SuperHouse/WMC/Images/2019-10-28 19.47.27.jpg

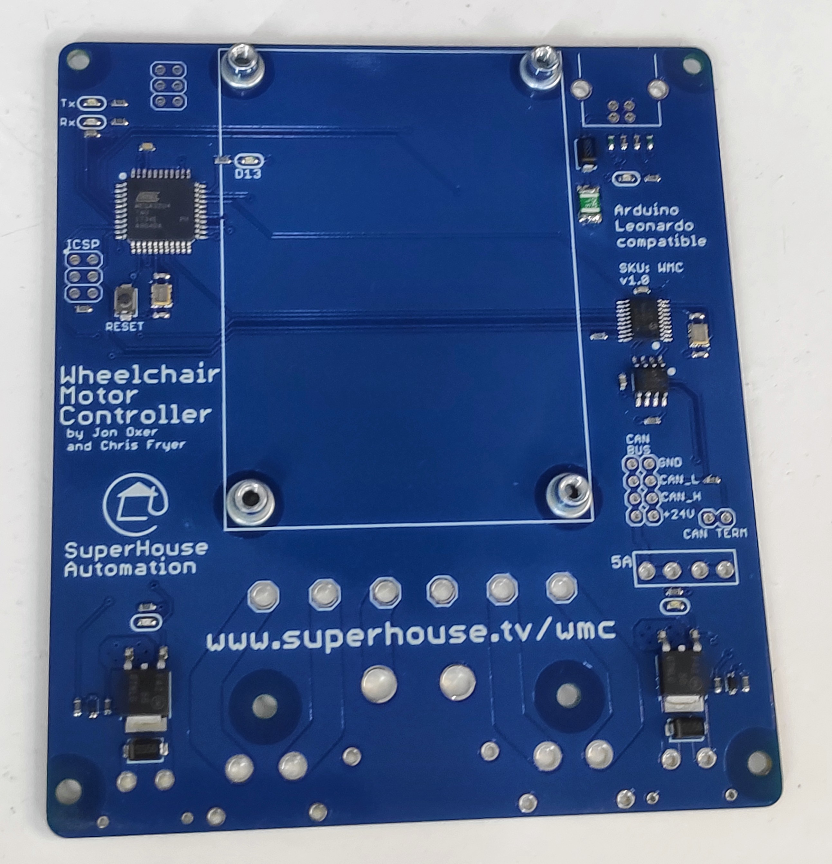
Images/2019-10-28 19.47.27.jpg
