SuperHouse/WMC/Images/2019-10-28 22.34.21.jpg

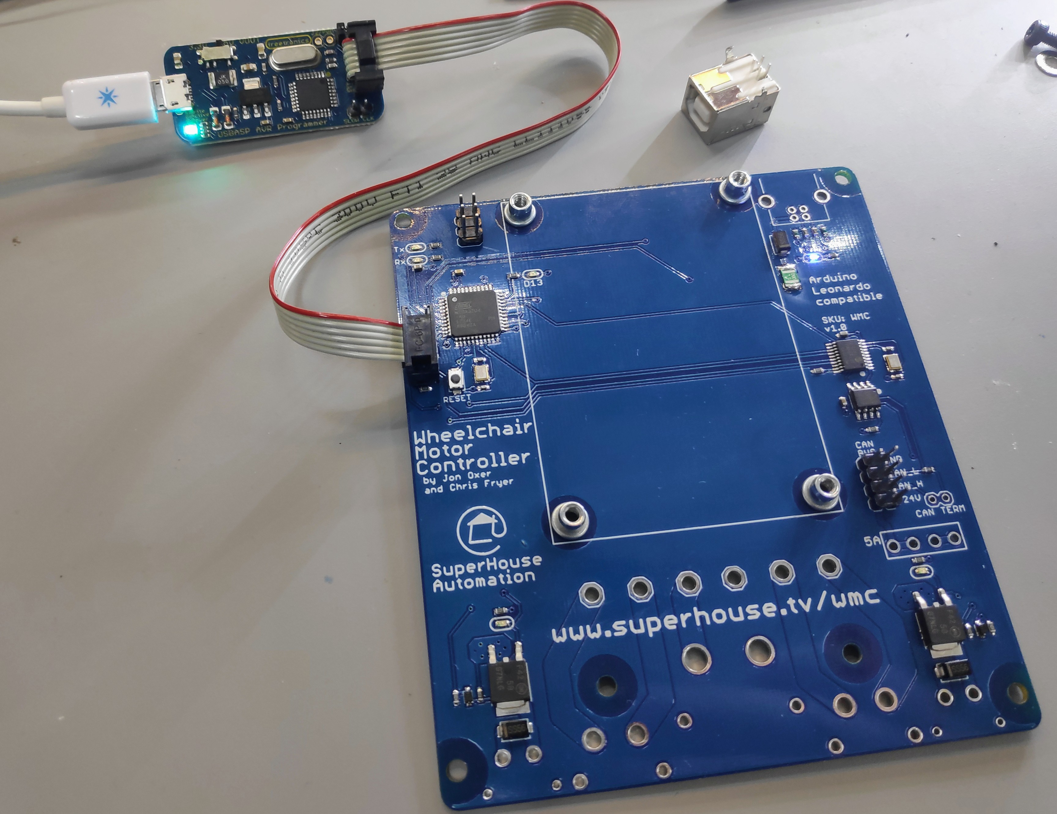
Images/2019-10-28 22.34.21.jpg
