SuperHouse/WMC/Images/2019-10-29 12.58.57.jpg

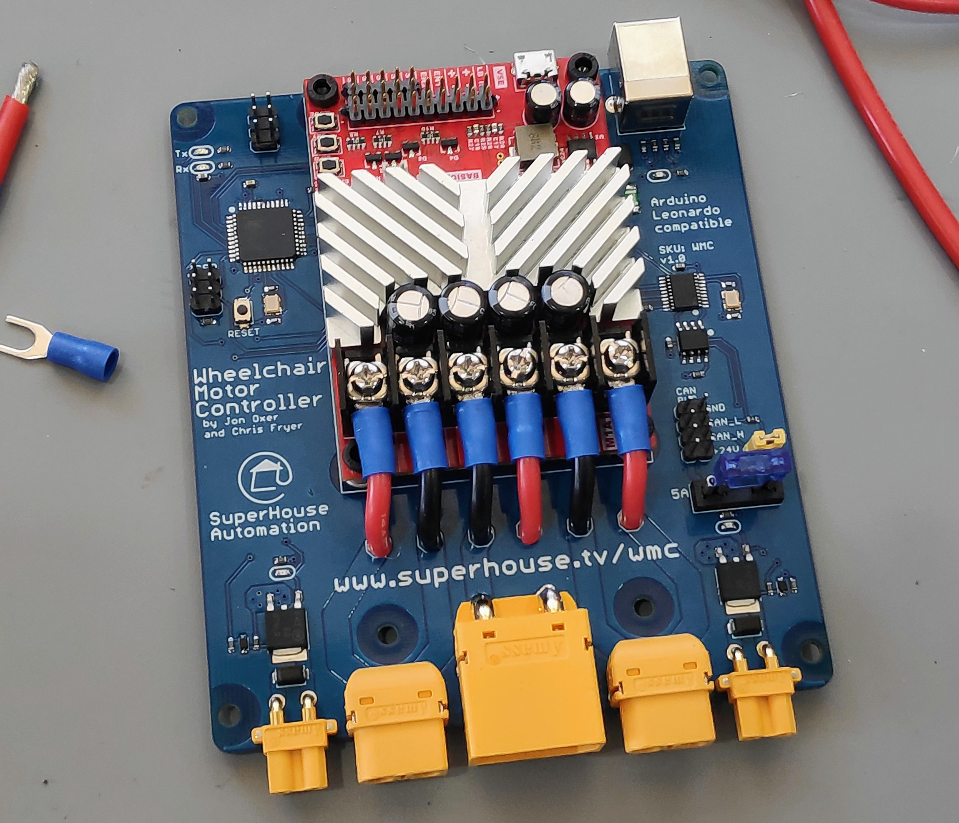
Images/2019-10-29 12.58.57.jpg
