SuperHouse/WMC/Images/2019-10-31 21.17.44.jpg

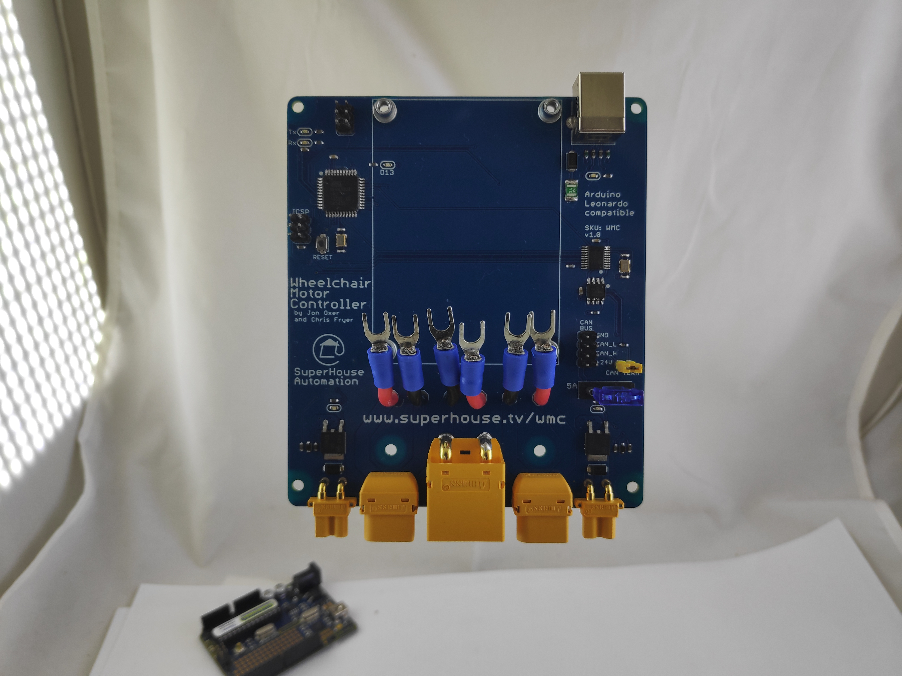
Images/2019-10-31 21.17.44.jpg
