SuperHouse/WMC/Images/2019-10-31 21.19.31.jpg

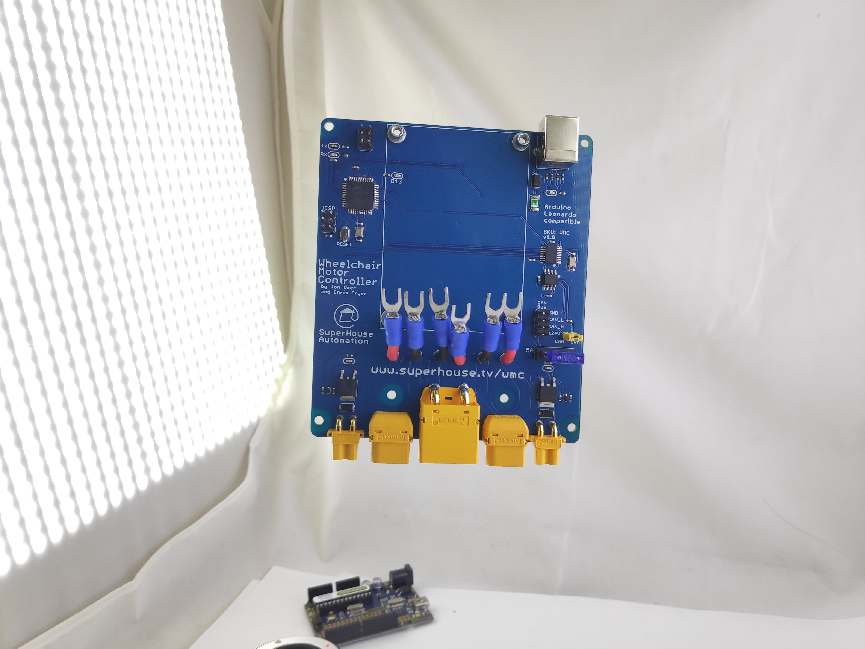
Images/2019-10-31 21.19.31.jpg
