SuperHouse/WMC/Images/2019-10-31 21.20.41.jpg

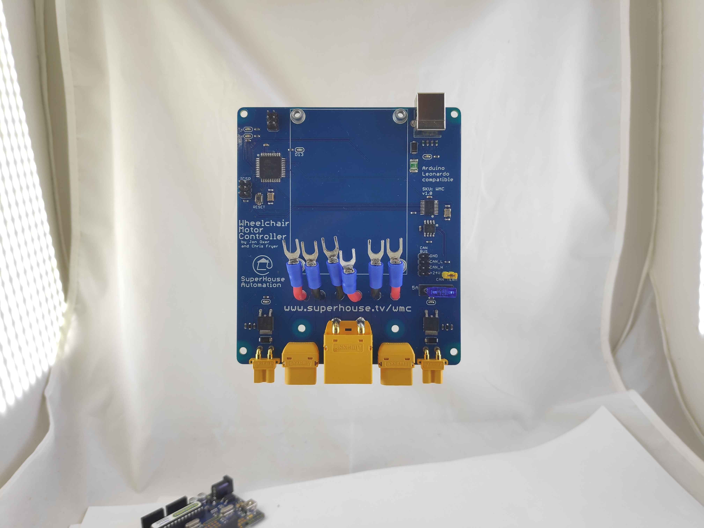
Images/2019-10-31 21.20.41.jpg
