SuperHouse/WMC/Images/2019-10-31 21.29.48.jpg

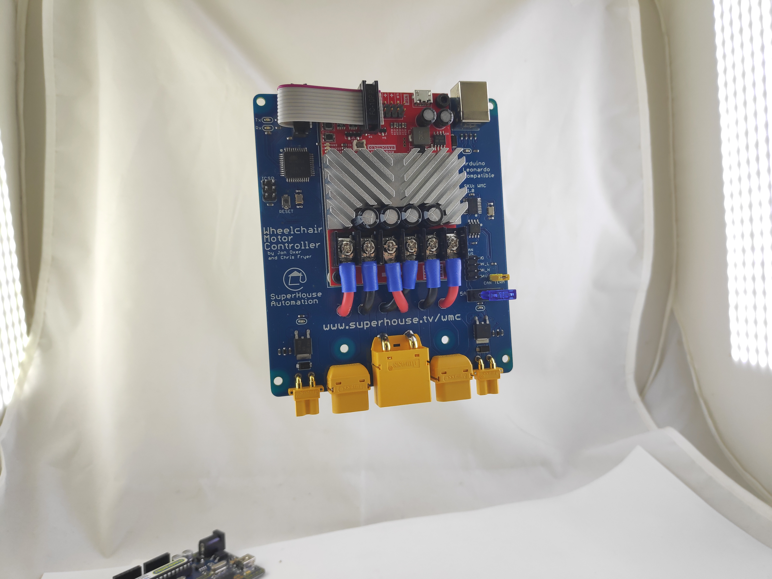
Images/2019-10-31 21.29.48.jpg
