SuperHouse/WMC/Images/2019-10-31 21.29.53.jpg

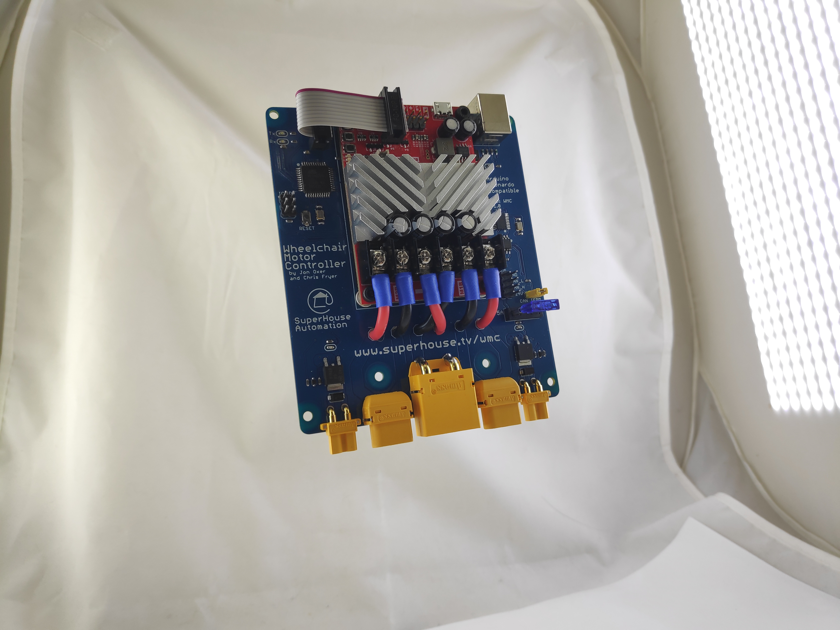
Images/2019-10-31 21.29.53.jpg
