SuperHouse/WMC/Images/2019-11-02 18.43.29.jpg

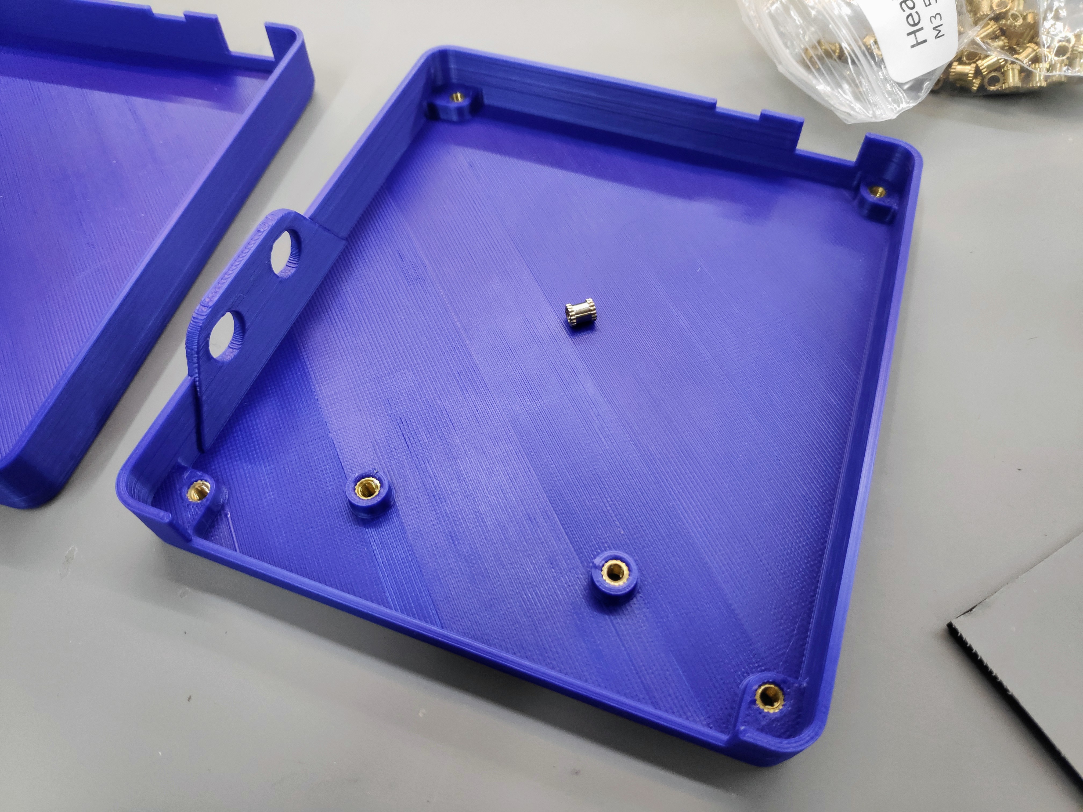
Images/2019-11-02 18.43.29.jpg
