SuperHouse/WMC/Images/2019-11-02 18.45.44.jpg

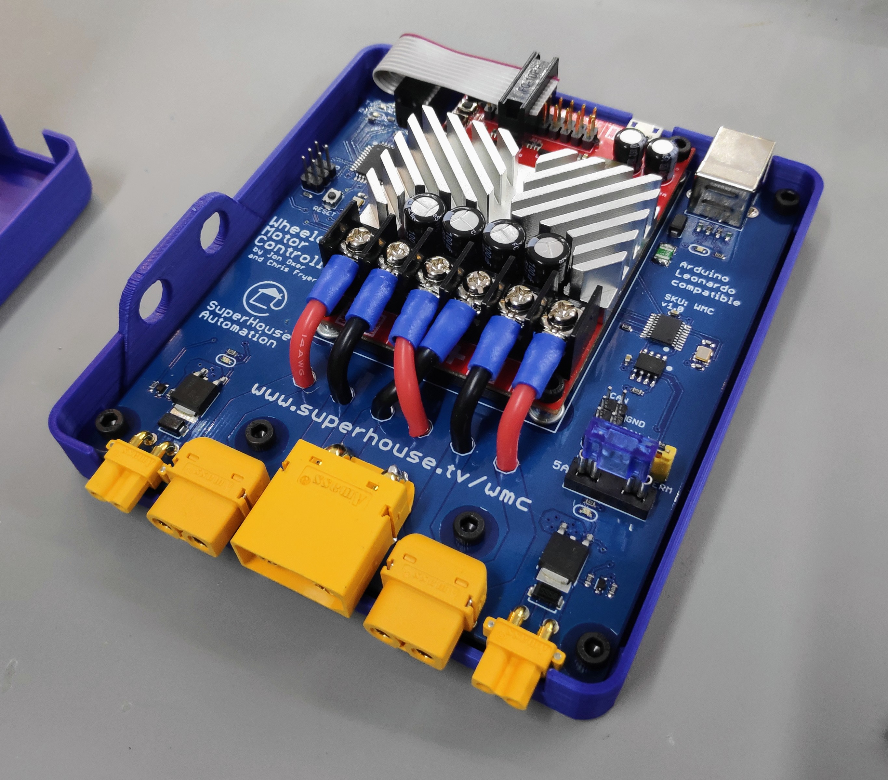
Images/2019-11-02 18.45.44.jpg
