SuperHouse/WMC/Images/2019-11-03 09.05.32.jpg

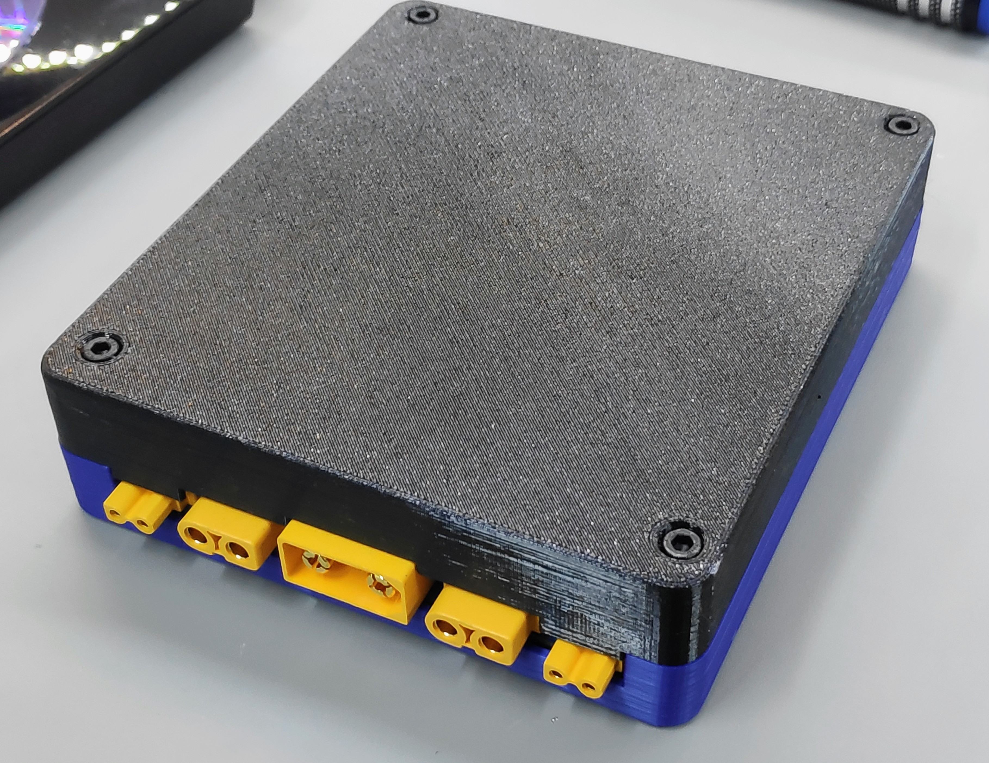
Images/2019-11-03 09.05.32.jpg
