SuperHouse/WMC/Images/2019-11-03 09.05.51.jpg

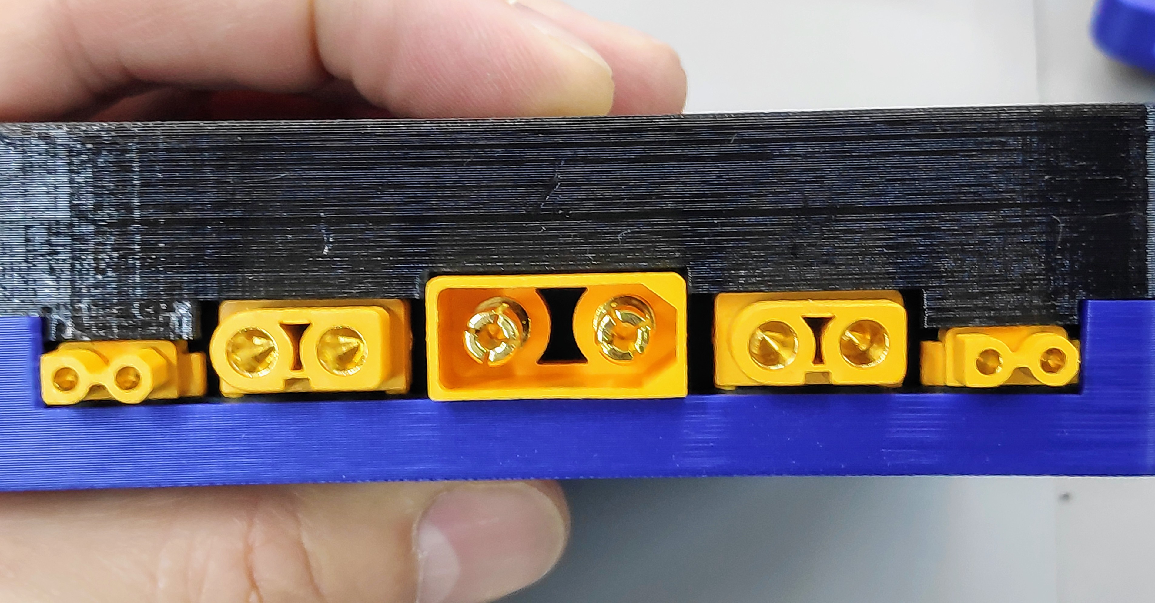
Images/2019-11-03 09.05.51.jpg
