SuperHouse/WMC/Images/2019-11-03 09.50.11.jpg

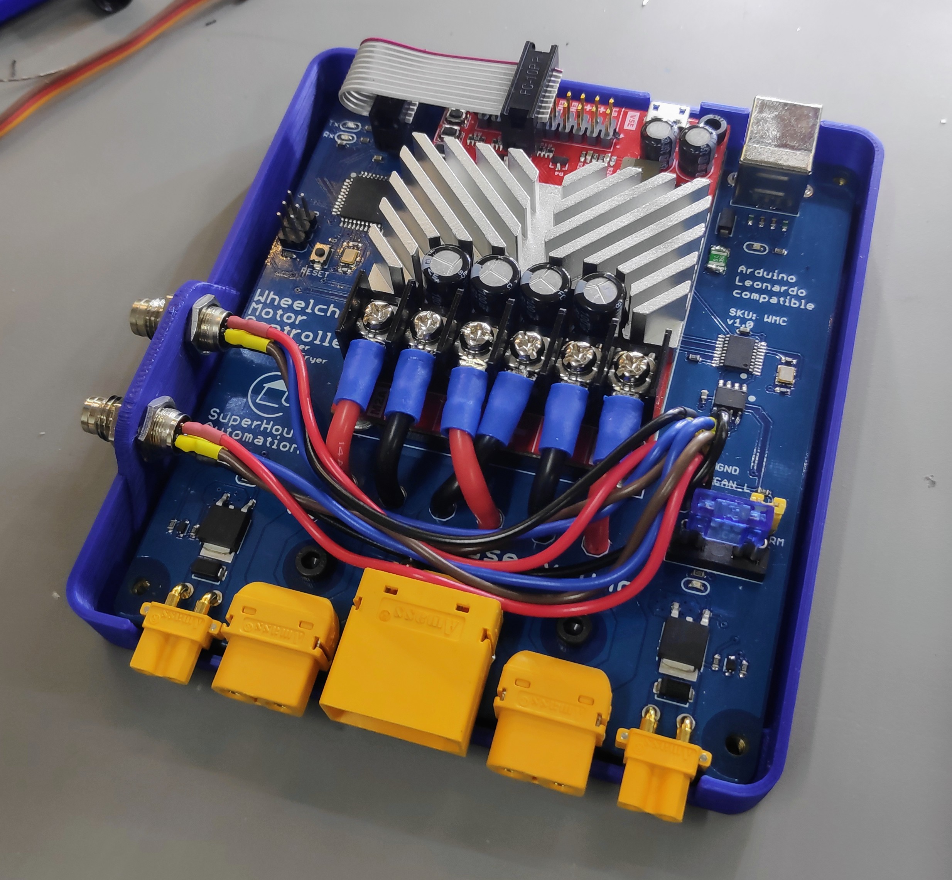
Images/2019-11-03 09.50.11.jpg
