SuperHouse/WMC/Images/2019-11-03 09.51.39.jpg

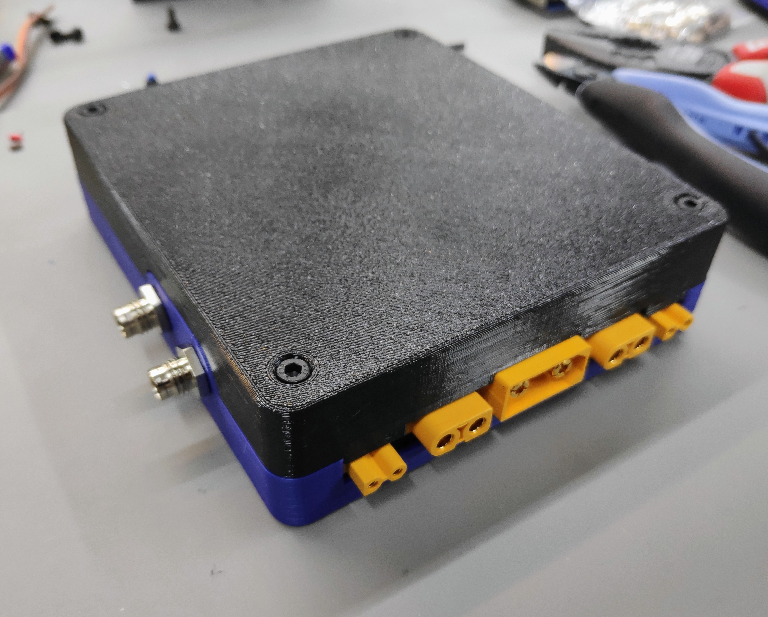
Images/2019-11-03 09.51.39.jpg
