SuperHouse/WMC/Images/2019-11-08 14.21.50.jpg

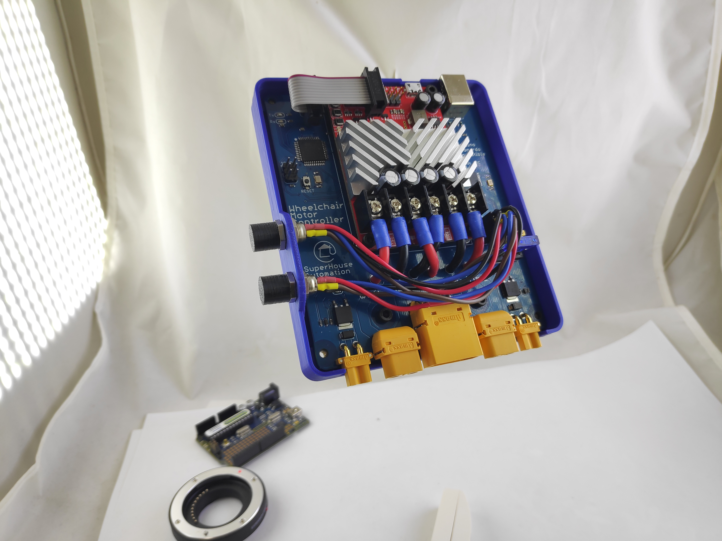
Images/2019-11-08 14.21.50.jpg
