SuperHouse/WMC/Images/WMC-v1_0-case-open.jpg

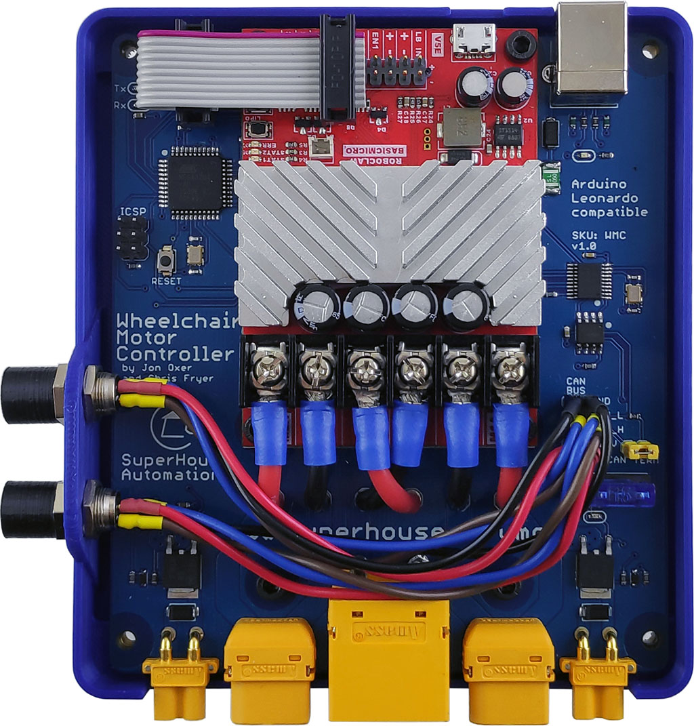
Images/WMC-v1_0-case-open.jpg
