SuperHouse/WMC/Images/WMC-v1_0-case_open_2.jpg

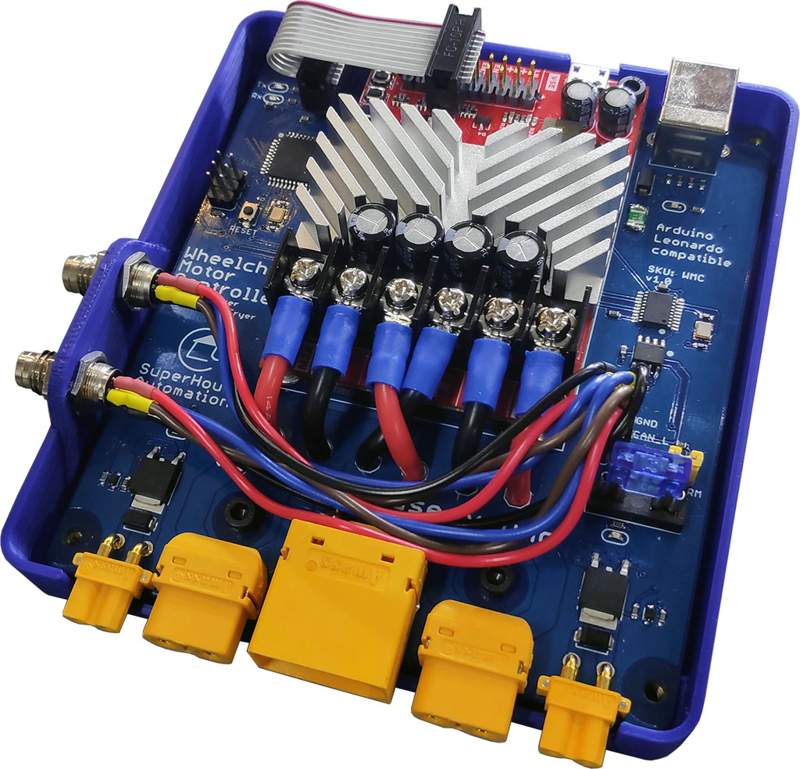
Images/WMC-v1_0-case_open_2.jpg
