SuperHouse/WMC/Images/WMC-v1_0-in-case-2.jpg

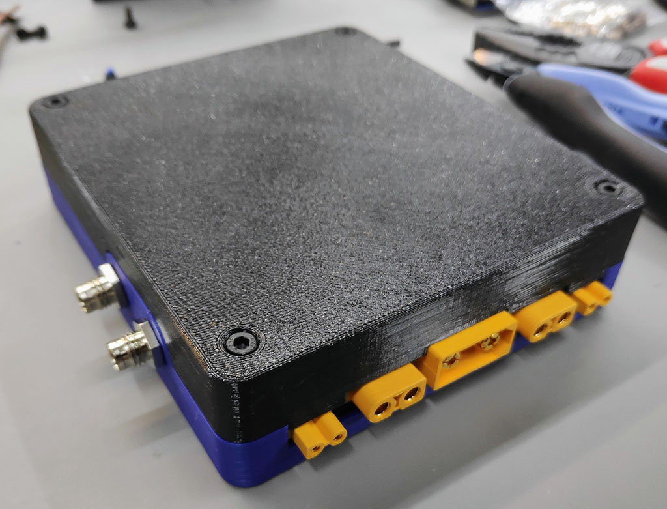
Images/WMC-v1_0-in-case-2.jpg
