SuperHouse/WMC/Images/WMC-v1_0-roboclaw-oblique.jpg

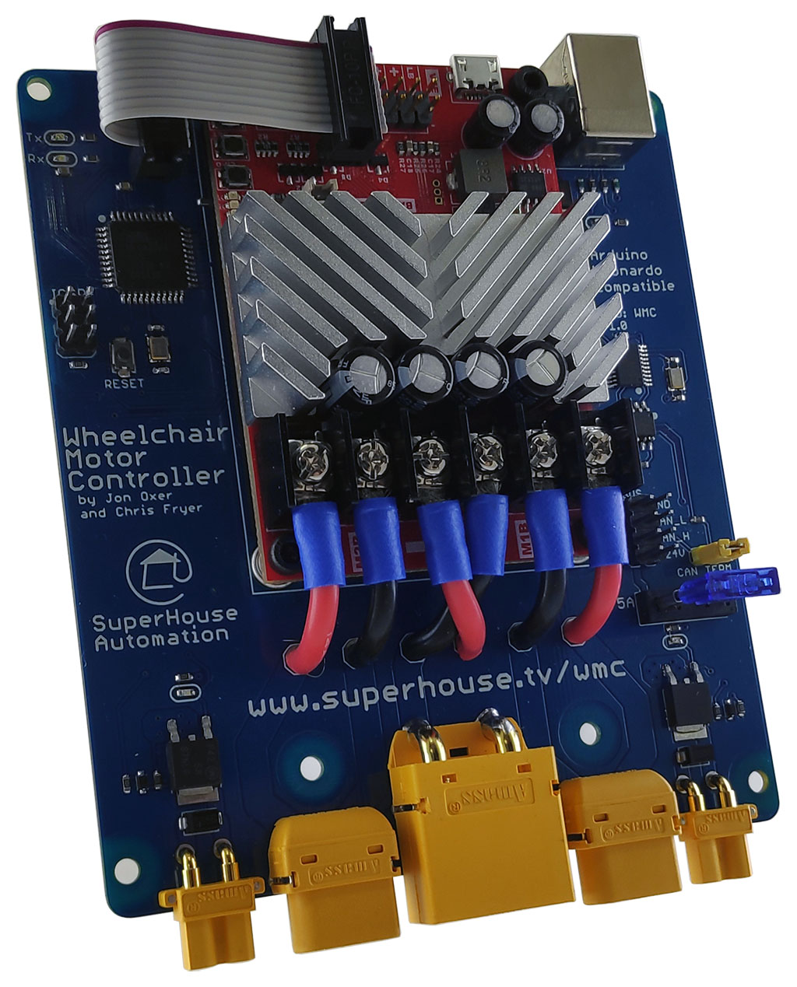
Images/WMC-v1_0-roboclaw-oblique.jpg
