SuperHouse/WMC/Firmware/RoboClawCAN/config.h

// Debug options
#define CAN_DEBUG false
#define OUTPUT_DEBUG true

#define LEFT_MOTOR_PIN  9
#define RIGHT_MOTOR_PIN 6

// Don't output more than this using PWM. Scale to make this 100% output
//#define MAX_OUTPUT_VALUE 180
//#define MID_OUTPUT_VALUE 90
//#define MIN_OUTPUT_VALUE  0

#define MAX_OUTPUT_VALUE 120
#define MID_OUTPUT_VALUE 90
#define MIN_OUTPUT_VALUE 60

#define REFERENCE_OFFSET_MULTIPLIER 0.013 // Magic number!
