SuperHouse/WMC/Firmware/roboclaw_python/roboclaw_python/roboclaw_python/roboclaw_readeeprom.py

import time
from roboclaw import Roboclaw

#Windows comport name
rc = Roboclaw("COM7",115200)
#Linux comport name
#rc = Roboclaw("/dev/ttyACM0",115200)

rc.Open()

#Get version string
for x in range(0,255):
	value = rc.ReadEeprom(0x80,x)
	print "EEPROM:",
	print x,
	print " ",
	if value[0]==False:
		print "Failed"
	else:
		print value[1]
